sjgray/CBM-MX-Keyboards/CBM2/CBM2-V1-R1/_pics/cbm2-02.jpg

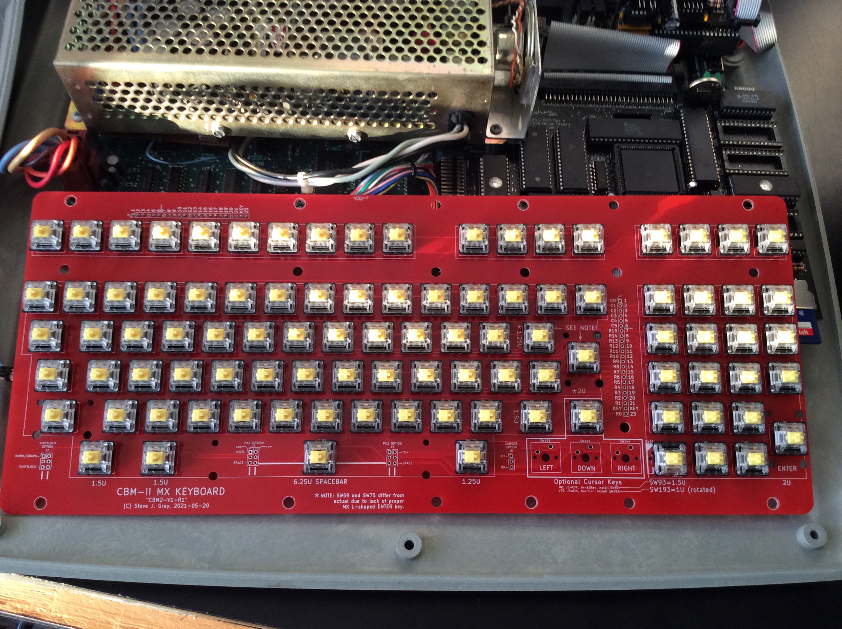
CBM2/CBM2-V1-R1/_pics/cbm2-02.jpg
