sjgray/CBM-MX-Keyboards/CBM2/CBM2-V1-R1/_pics/render-2021-05-17.jpg

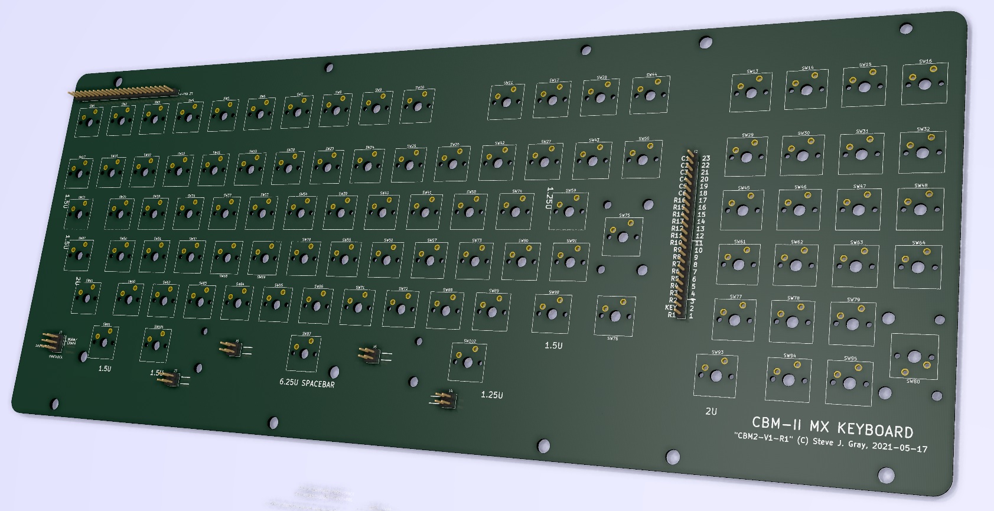
CBM2/CBM2-V1-R1/_pics/render-2021-05-17.jpg
