sjgray/CBM-MX-Keyboards/CBM2/CBM2-V1-R1/_pics/sch.png

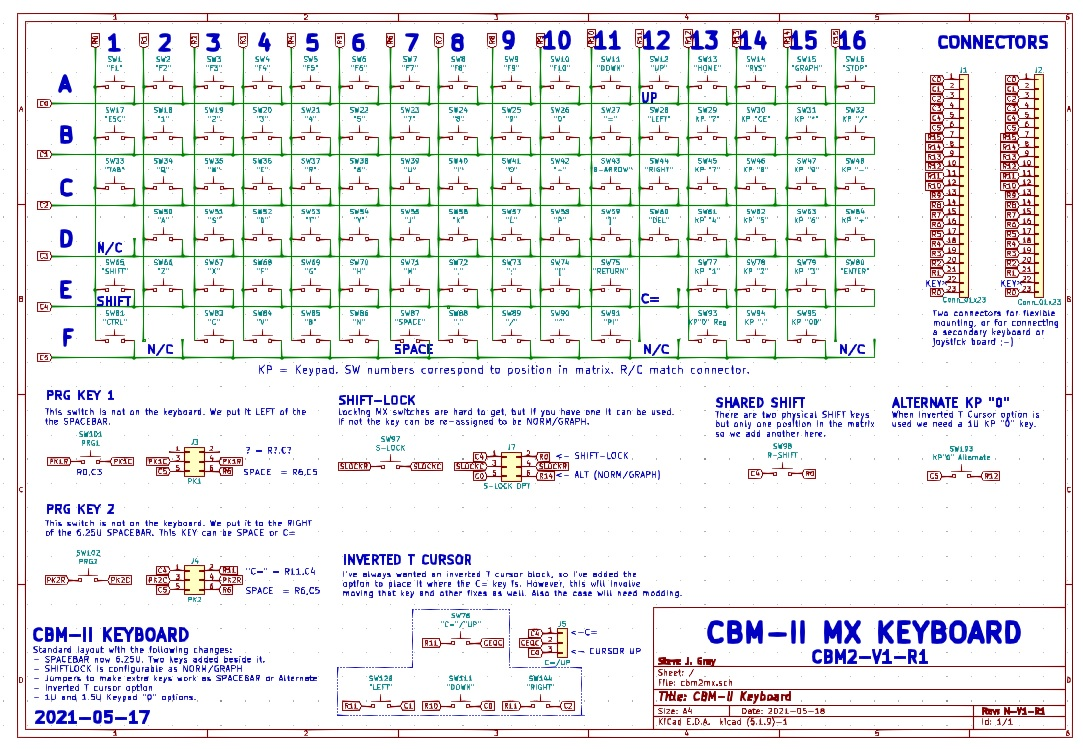
CBM2/CBM2-V1-R1/_pics/sch.png
