sjgray/CBM-MX-Keyboards/MX-Toggle/pics/2025-12-02-Boards arrive.jpg

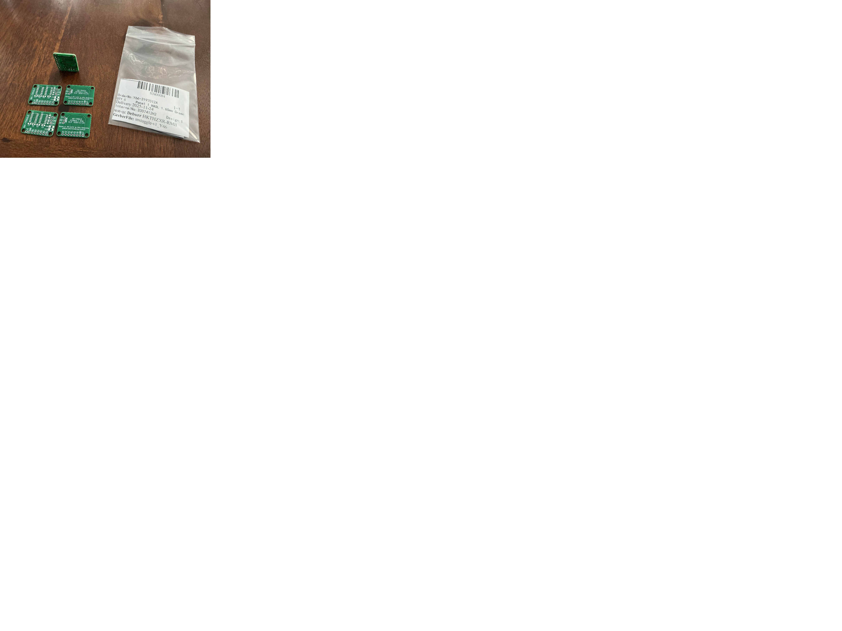
MX-Toggle/pics/2025-12-02-Boards arrive.jpg
