sjgray/CBM-MX-Keyboards/MX-Toggle/pics/2025-12-04-Board-back.jpg

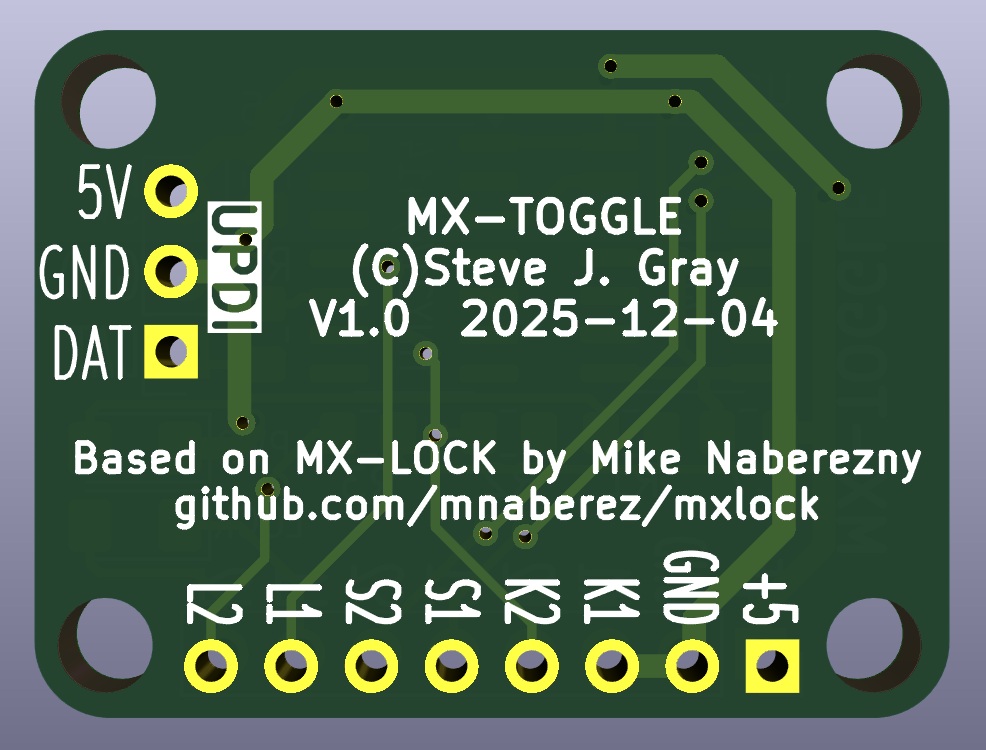
MX-Toggle/pics/2025-12-04-Board-back.jpg
