sjgray/CBM-MX-Keyboards/MX-Toggle/pics/2025-12-04-Completed board.jpg

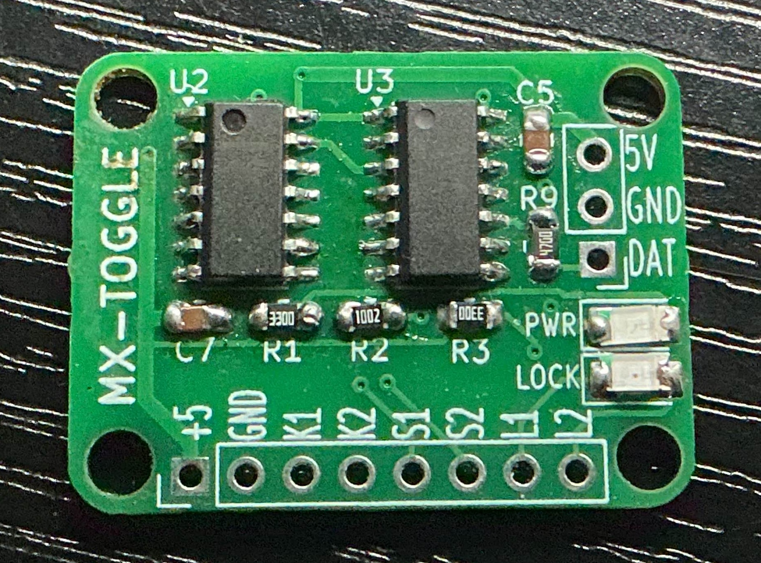
MX-Toggle/pics/2025-12-04-Completed board.jpg
