sjgray/CBM-MX-Keyboards/PET-B/B-V1-R1/_Pics/b-v1-r1-layout.png

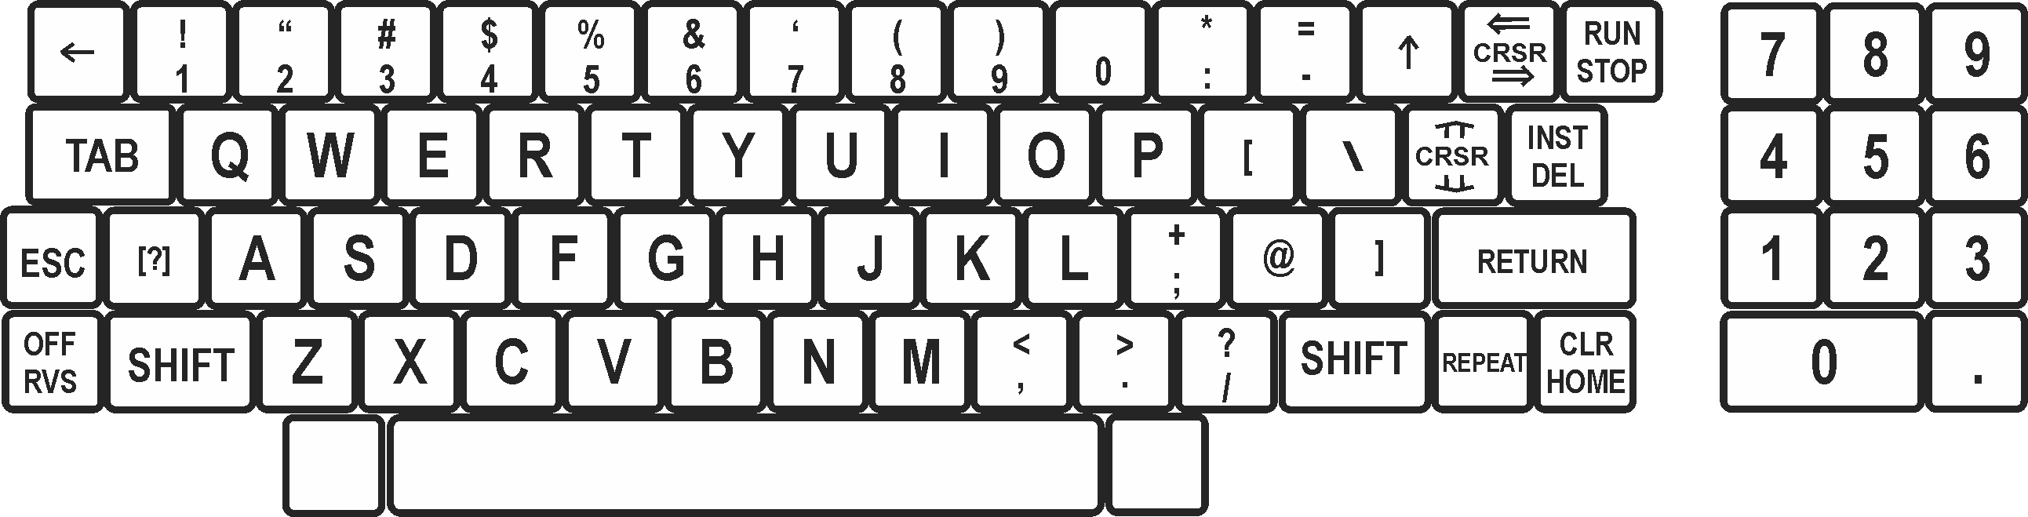
PET-B/B-V1-R1/_Pics/b-v1-r1-layout.png
