sjgray/CBM-MX-Keyboards/PET-B/B-V1-R2/pics/B-V1-R2-02-crop.jpg

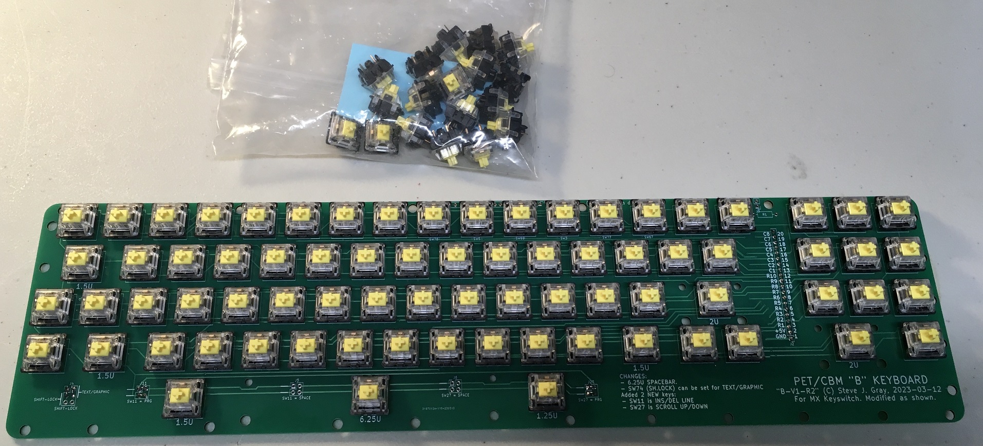
PET-B/B-V1-R2/pics/B-V1-R2-02-crop.jpg
