sjgray/CBM-MX-Keyboards/PET-B/B-V1-R2/pics/pic.png

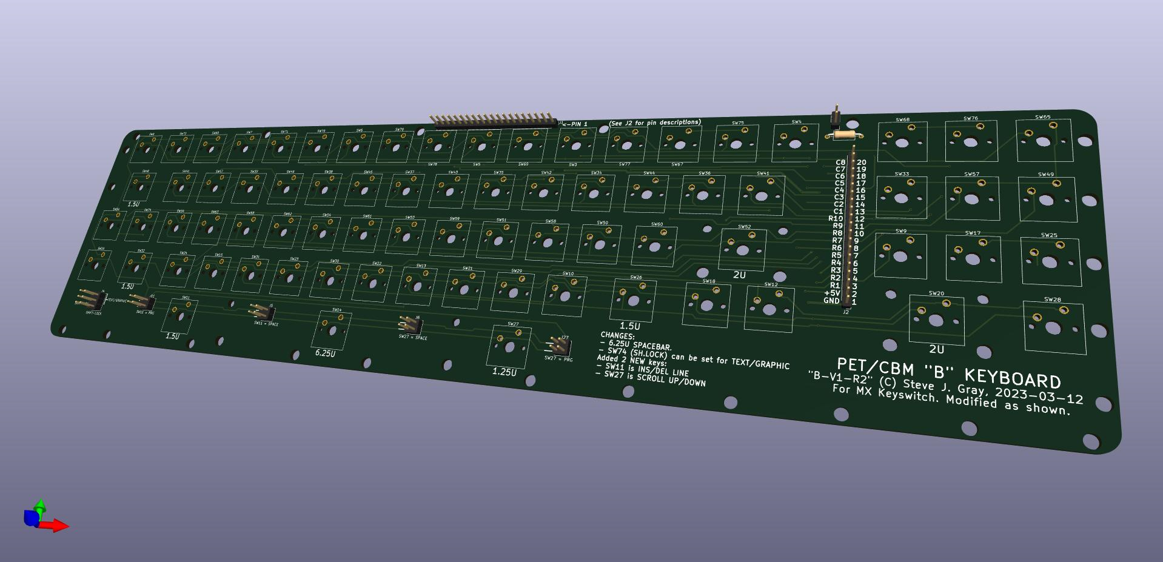
PET-B/B-V1-R2/pics/pic.png
