sjgray/CBM-MX-Keyboards/PET-N/N-V1-R1/_Pics/render-2020-12-18-100h.jpg

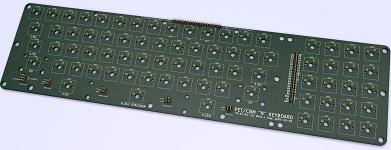
PET-N/N-V1-R1/_Pics/render-2020-12-18-100h.jpg
