sjgray/CBM-MX-Keyboards/PET-N/N-V1-R1/_Pics/routing-2020-12-18.jpg

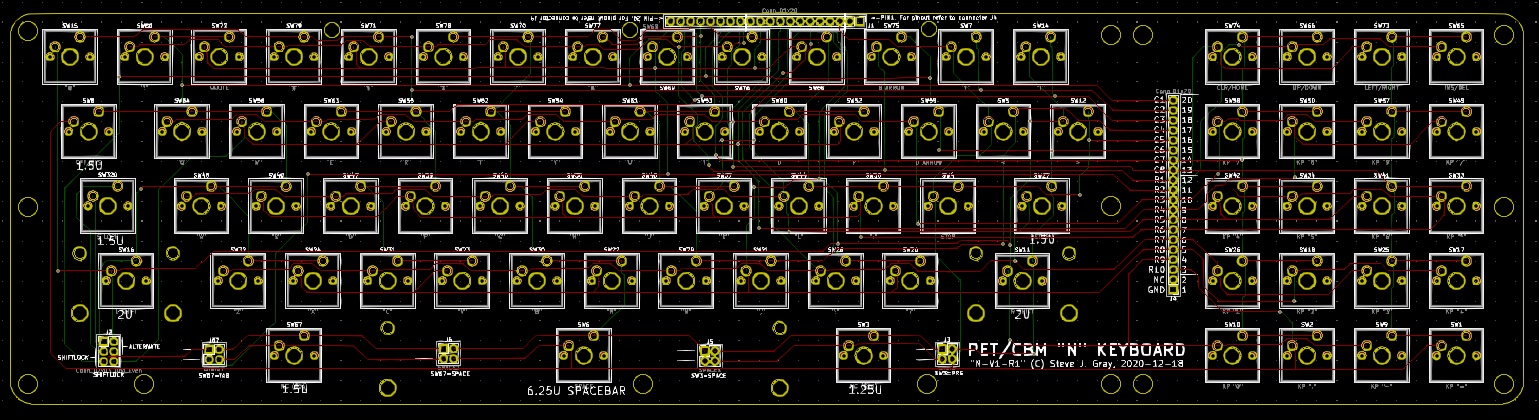
PET-N/N-V1-R1/_Pics/routing-2020-12-18.jpg
