sjgray/CBM-MX-Keyboards/scans/C16-150.jpg

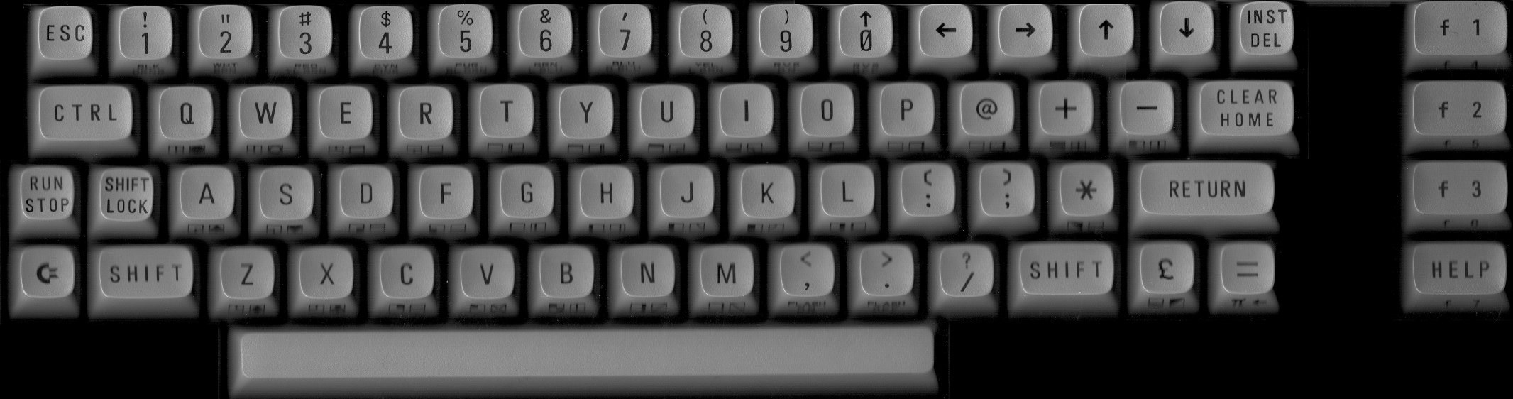
scans/C16-150.jpg
