sjgray/CBM-MX-Keyboards/scans/c128-150dpi.jpg

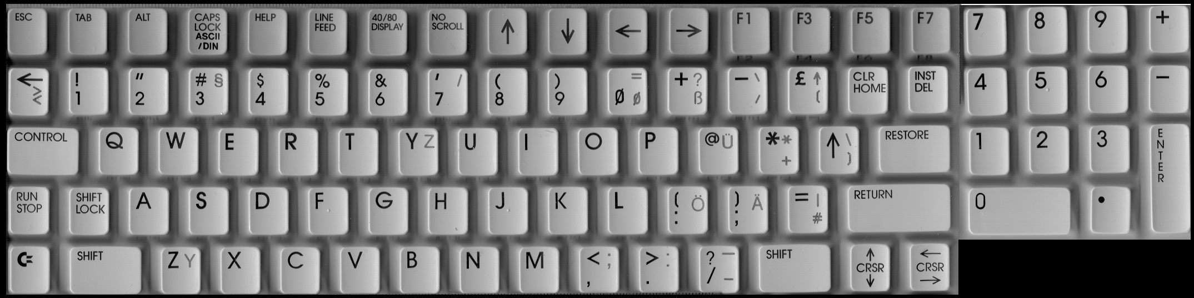
scans/c128-150dpi.jpg
