sjgray/CBM-MX-Keyboards/scans/cbm2-150dpi.jpg

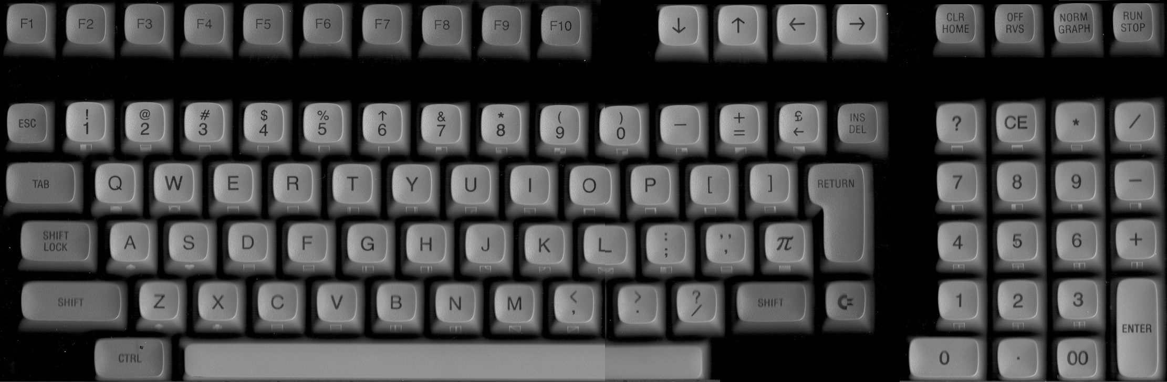
scans/cbm2-150dpi.jpg
