sjgray/CBM-MX-Keyboards/scans/clcd-scan.jpg

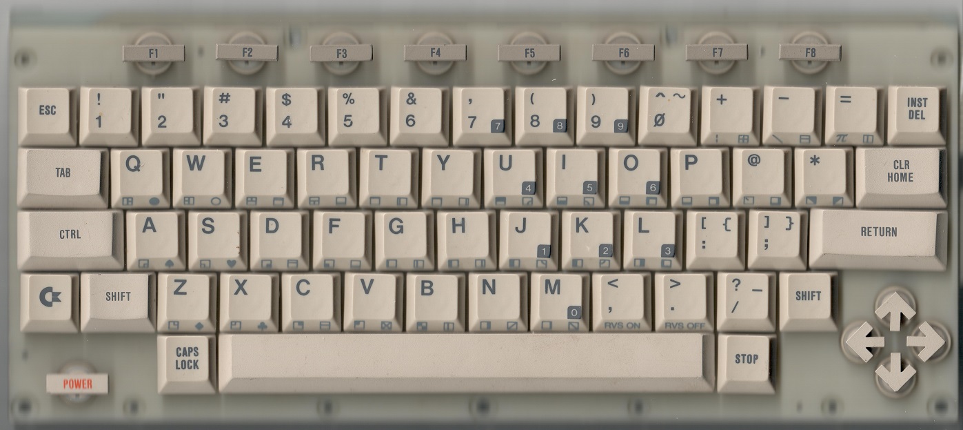
scans/clcd-scan.jpg
