sjgray/CBM-MX-Keyboards/scans/plus4-300dpi.jpg

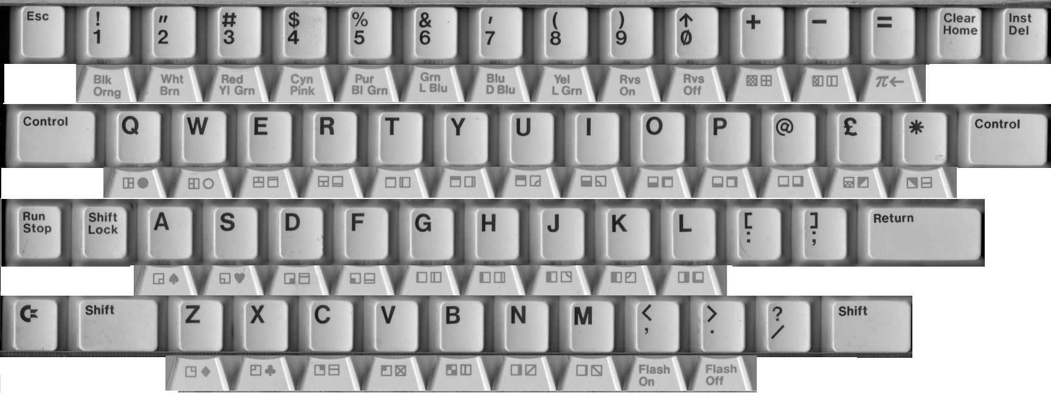
scans/plus4-300dpi.jpg
