sjgray/CBM-MX-Keyboards/scans/sx64-150dpi.jpg

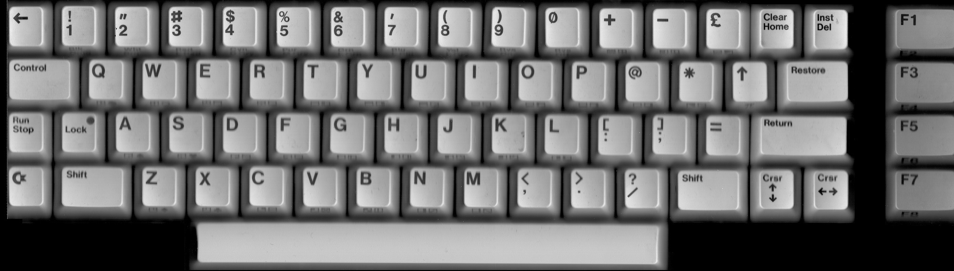
scans/sx64-150dpi.jpg
